crakeron/Projet_CM/Catia_GPZ500/Drawing/Drawing engrenage.jpg

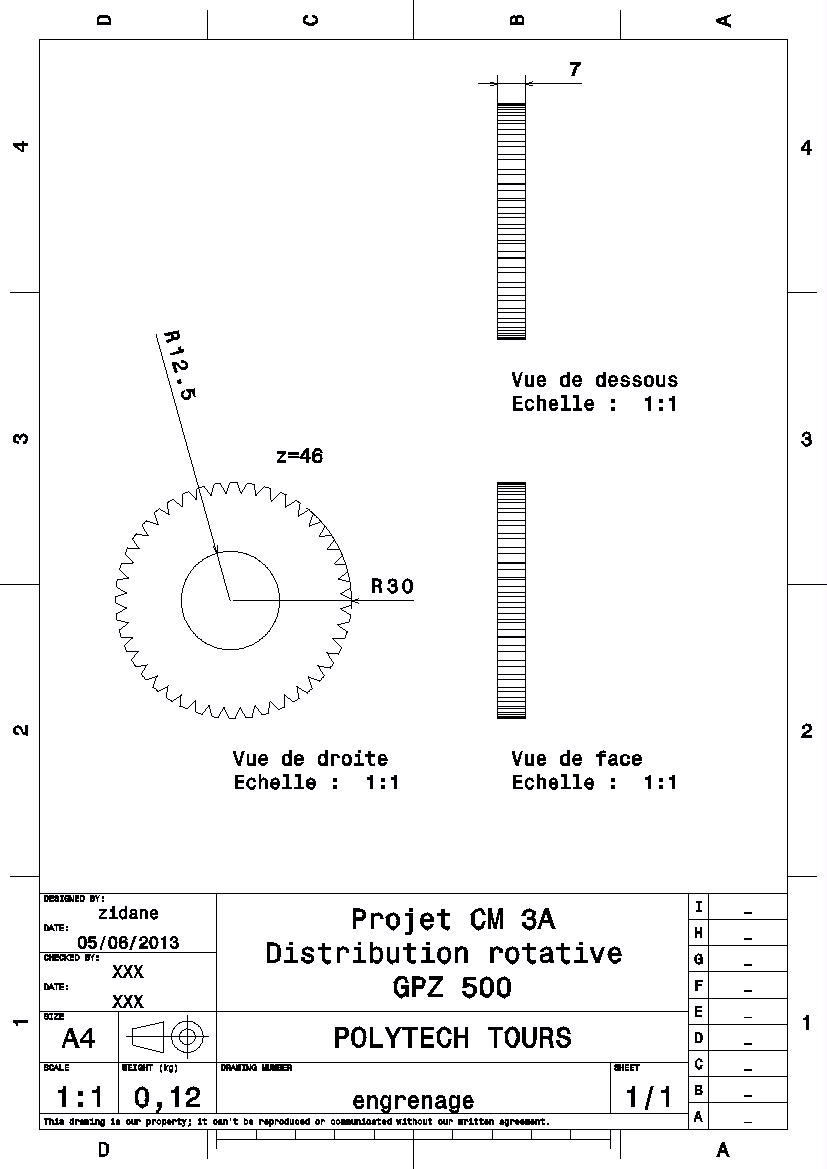
Catia_GPZ500/Drawing/Drawing engrenage.jpg
