crakeron/Projet_CM/Catia_GPZ500/Drawing/DrawingCHAPEAUX.jpg

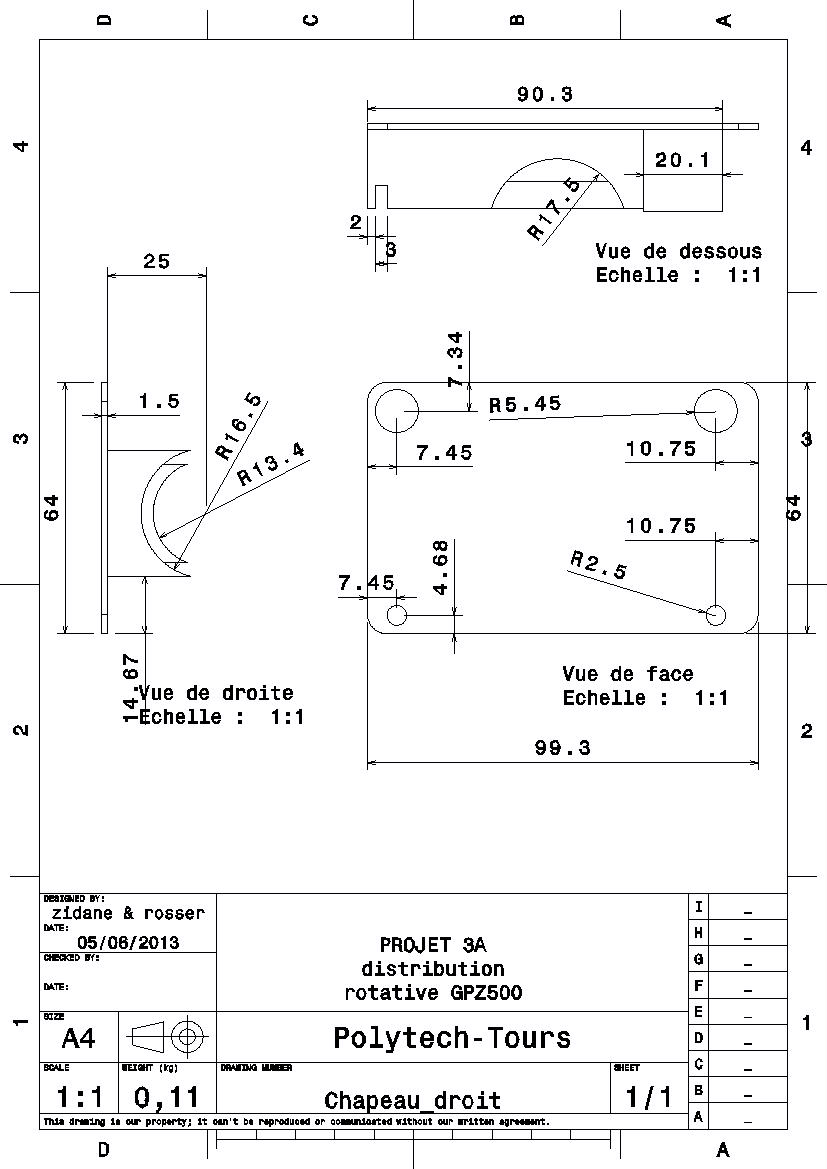
Catia_GPZ500/Drawing/DrawingCHAPEAUX.jpg
