crakeron/Projet_CM/Catia_GPZ500/Drawing/Drawingtube.jpg

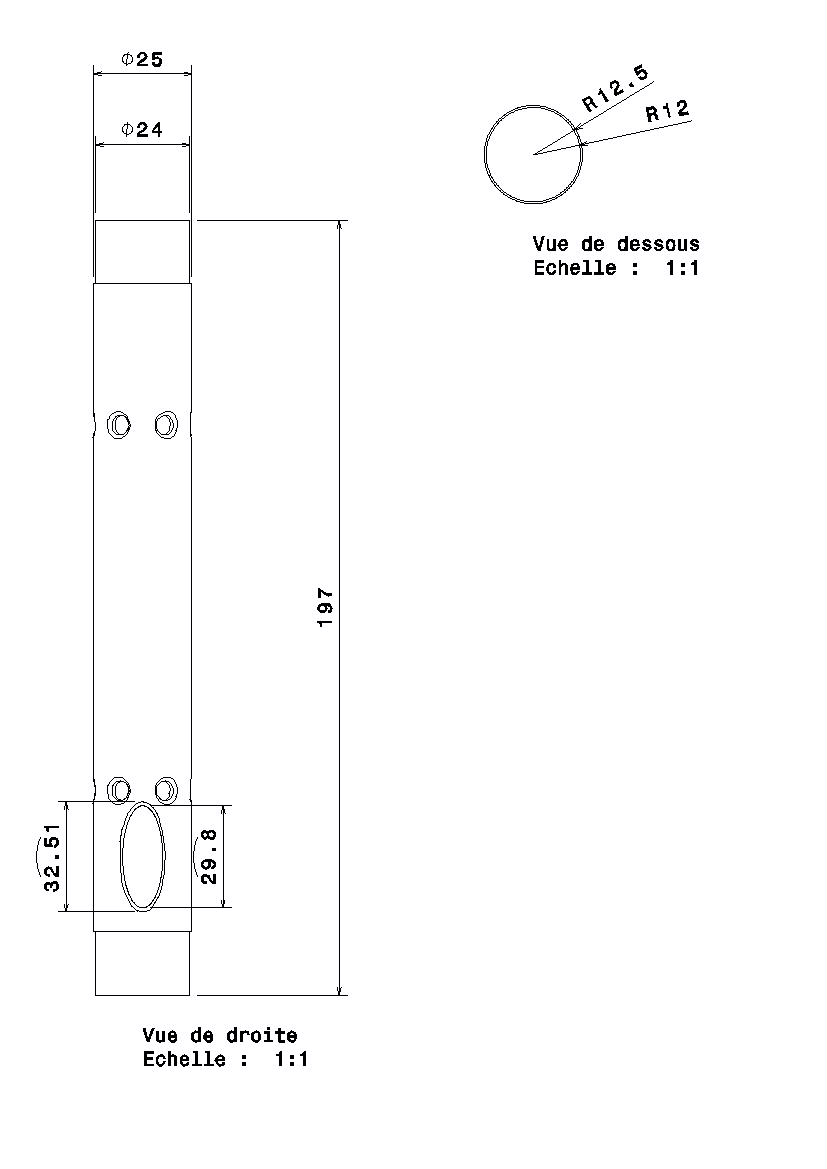
Catia_GPZ500/Drawing/Drawingtube.jpg
