crakeron/Projet_CM/Catia_GPZ500/Photos/7mai.png

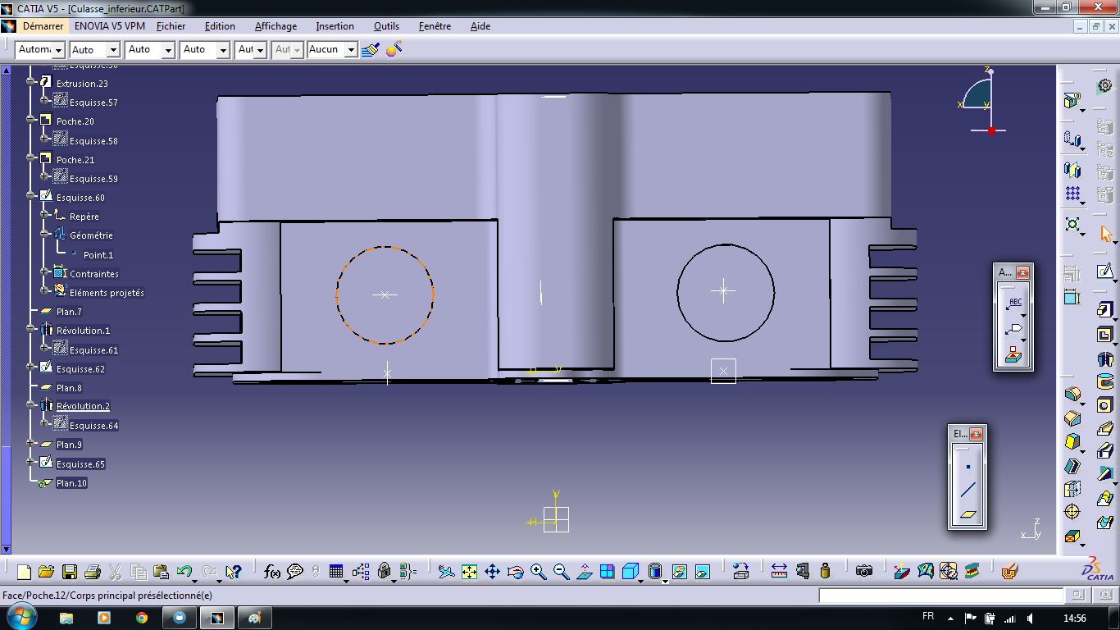
Catia_GPZ500/Photos/7mai.png
