crakeron/Projet_CM/Catia_GPZ500/Photos/7mai_2.png

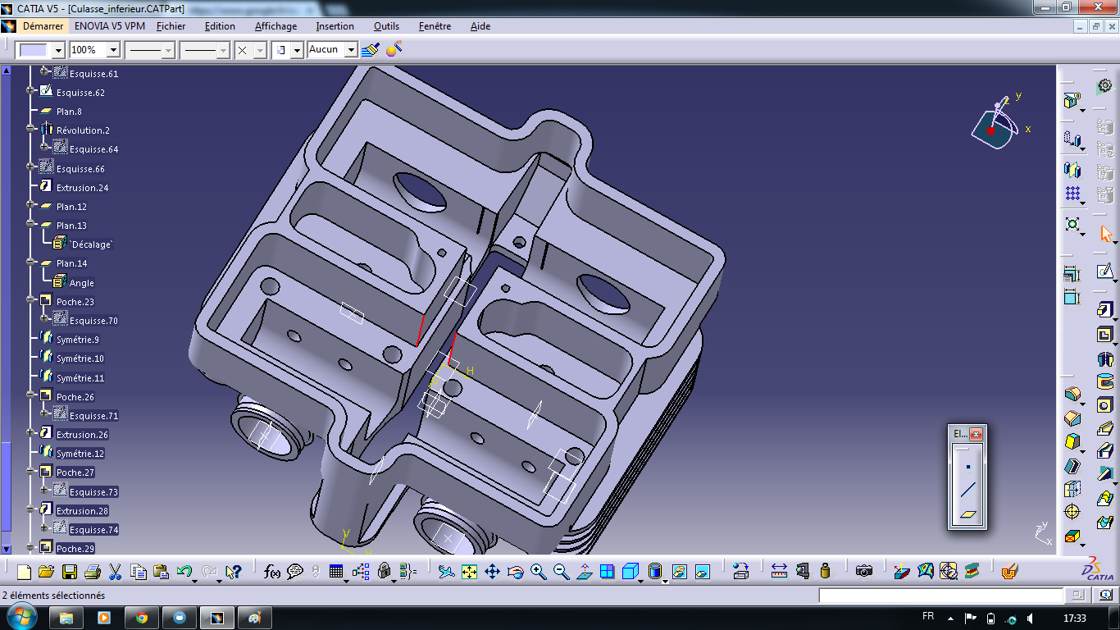
Catia_GPZ500/Photos/7mai_2.png
