crakeron/Projet_CM/Catia_GPZ500/Photos/15mai1.png

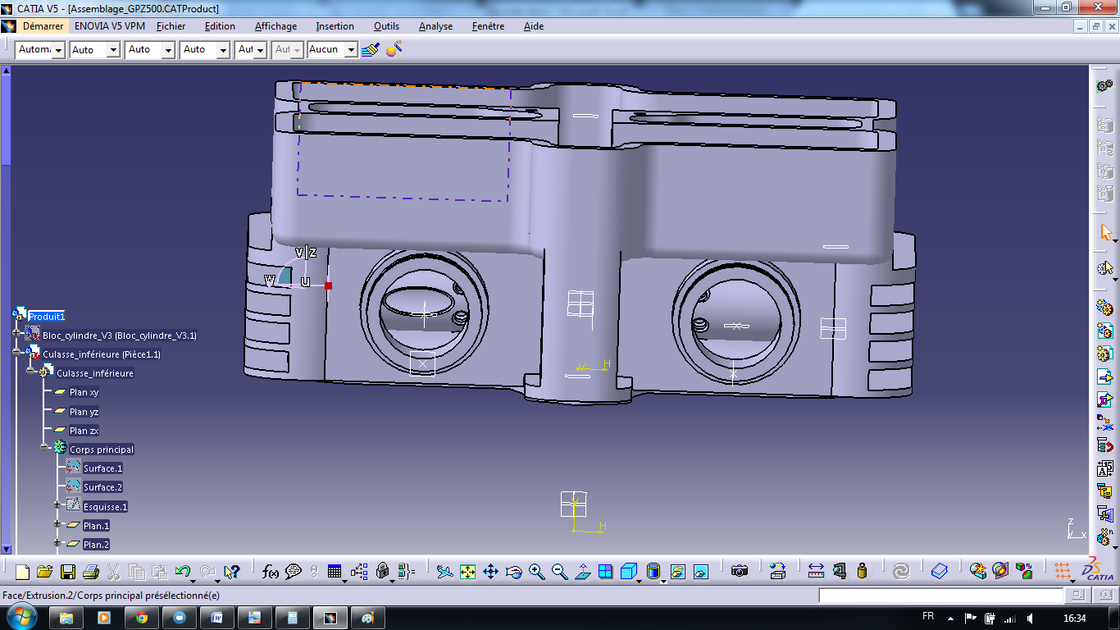
Catia_GPZ500/Photos/15mai1.png
