crakeron/Projet_CM/Catia_GPZ500/Photos/16mai2.png

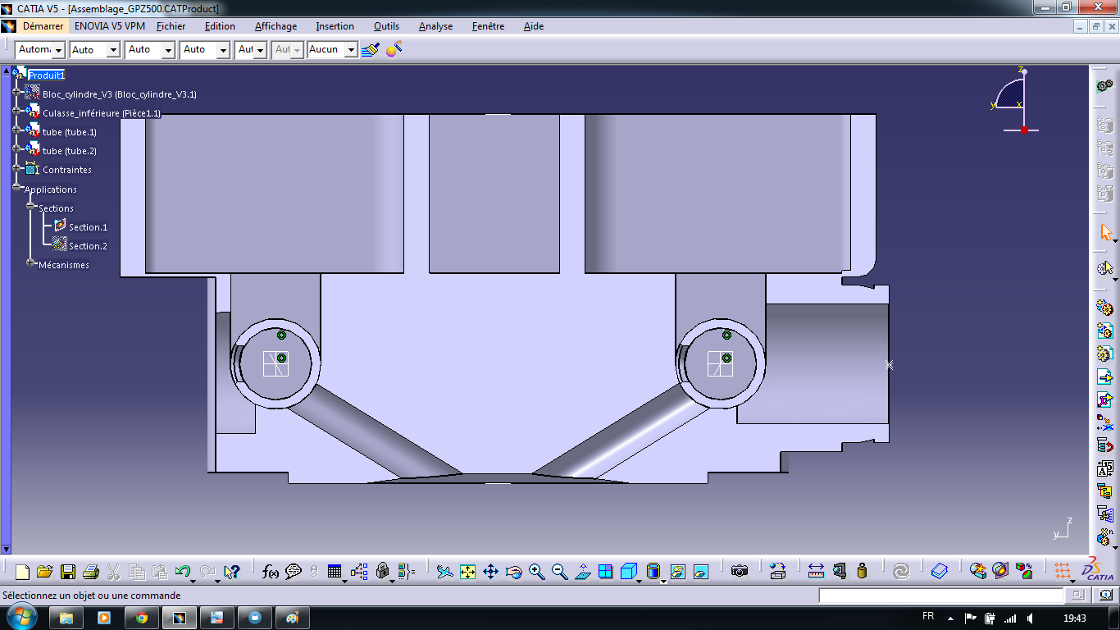
Catia_GPZ500/Photos/16mai2.png
