crakeron/Projet_CM/Catia_GPZ500/Photos/31mai1.png

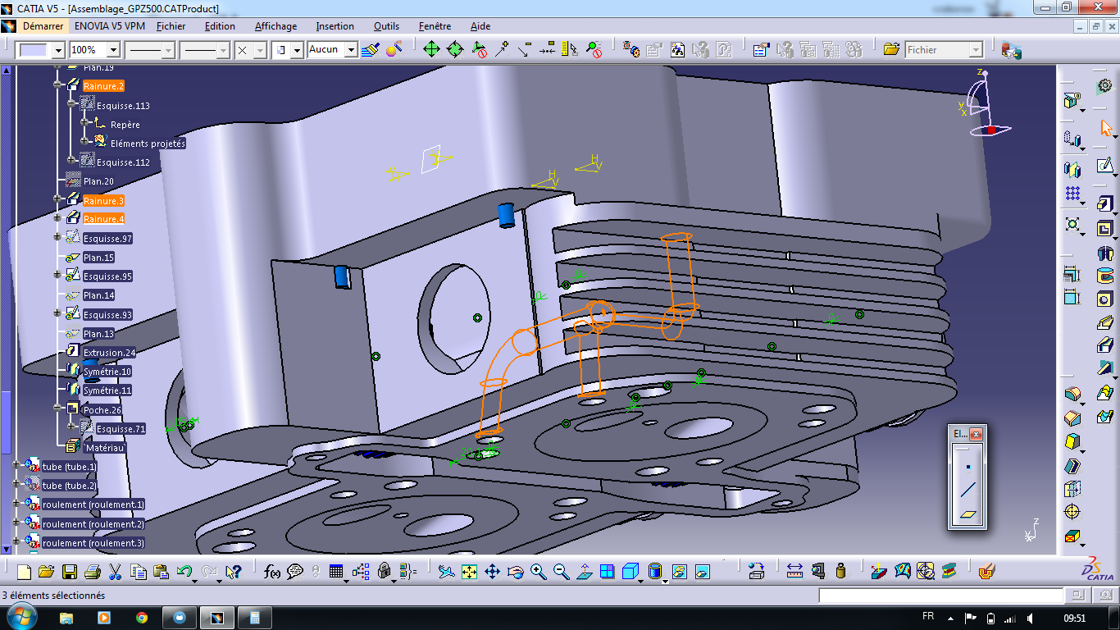
Catia_GPZ500/Photos/31mai1.png
