crakeron/Projet_CM/Catia_GPZ500/Photos/bloc cylin.bmp

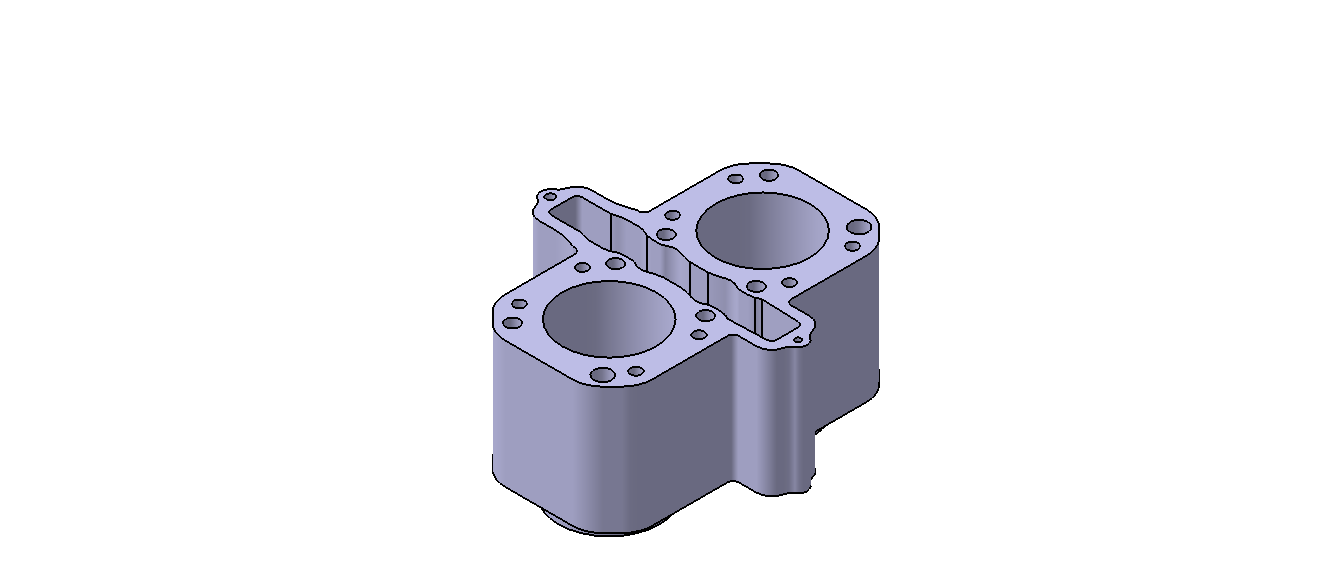
Catia_GPZ500/Photos/bloc cylin.bmp
