crakeron/Projet_CM/Catia_GPZ500/Photos/Bloc Cylindre/Bloc_Cylindre_Profil_Normale.jpg

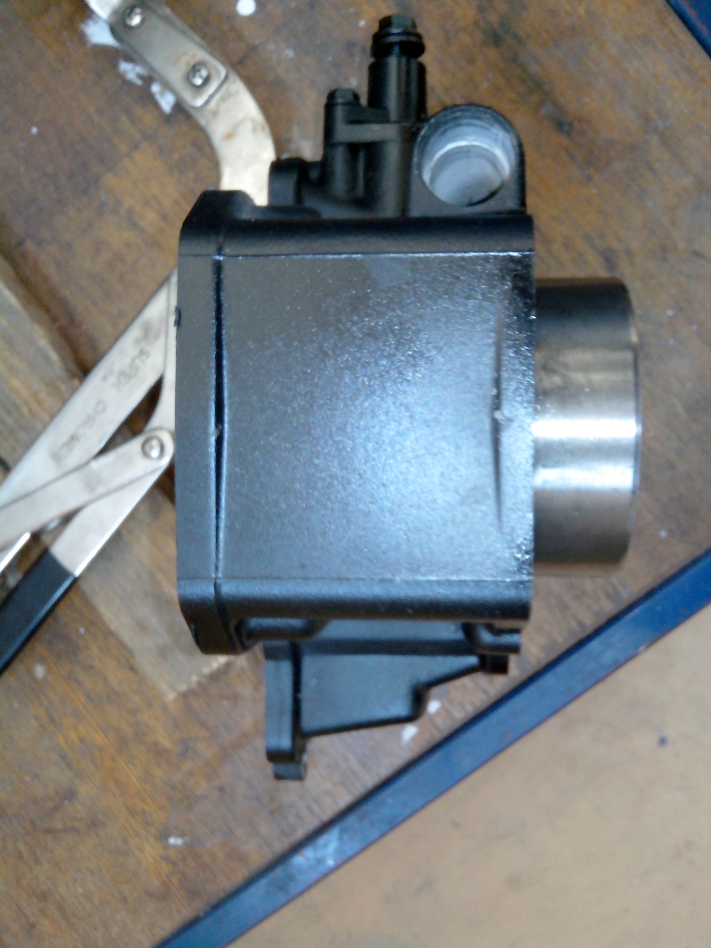
Catia_GPZ500/Photos/Bloc Cylindre/Bloc_Cylindre_Profil_Normale.jpg
