crakeron/Projet_CM/Catia_GPZ500/Photos/Bloc_cylindre cotation.jpg

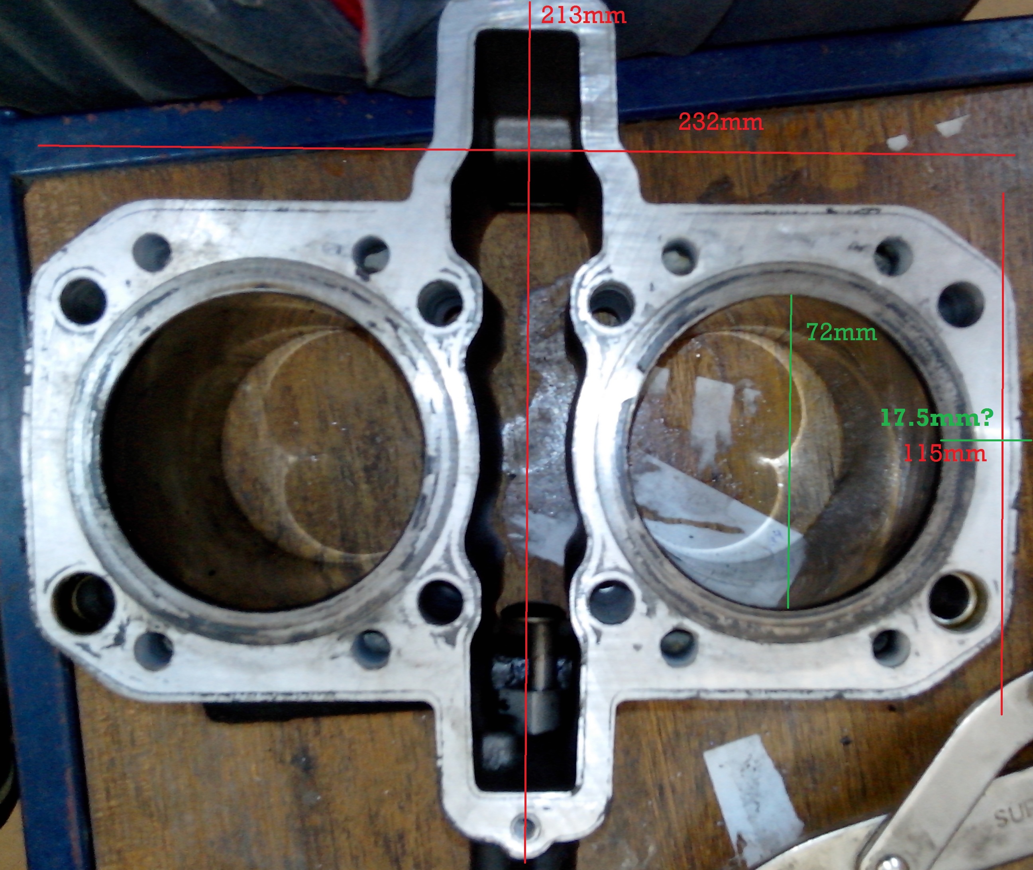
Catia_GPZ500/Photos/Bloc_cylindre cotation.jpg
