crakeron/Projet_CM/Catia_GPZ500/Photos/Culasse/Culasse_dessous.jpg

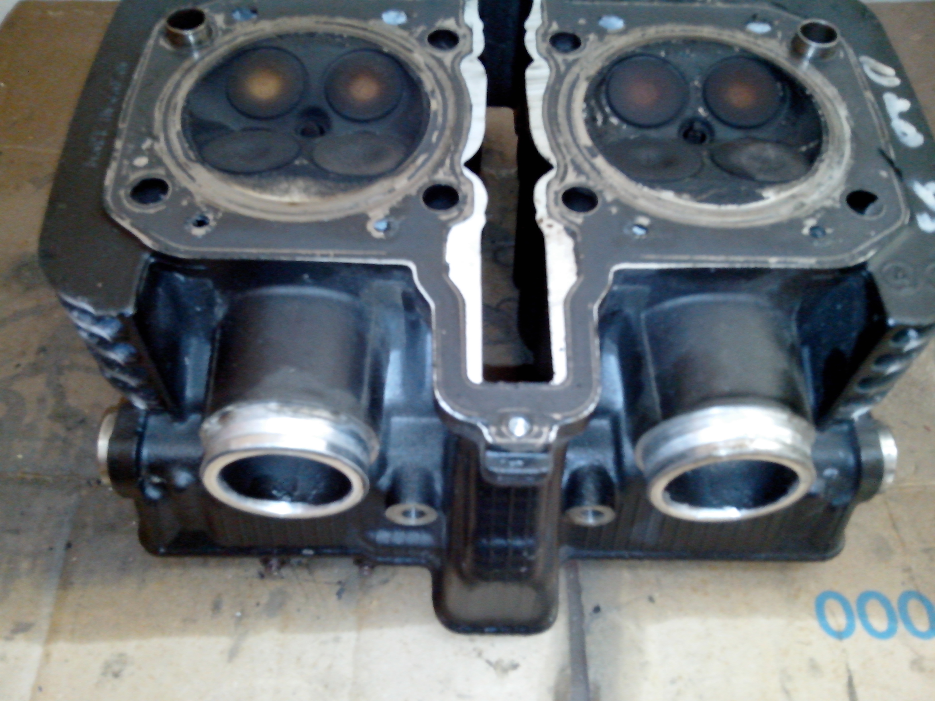
Catia_GPZ500/Photos/Culasse/Culasse_dessous.jpg
