crakeron/Projet_CM/Catia_GPZ500/Photos/Culasse/Culasse_dessous_normale.jpg

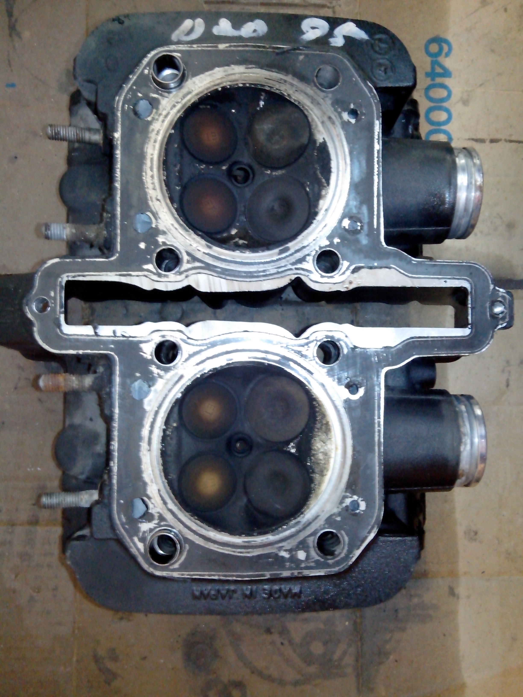
Catia_GPZ500/Photos/Culasse/Culasse_dessous_normale.jpg
