crakeron/Projet_CM/Catia_GPZ500/Photos/Culasse/Culasse_Normale.jpg

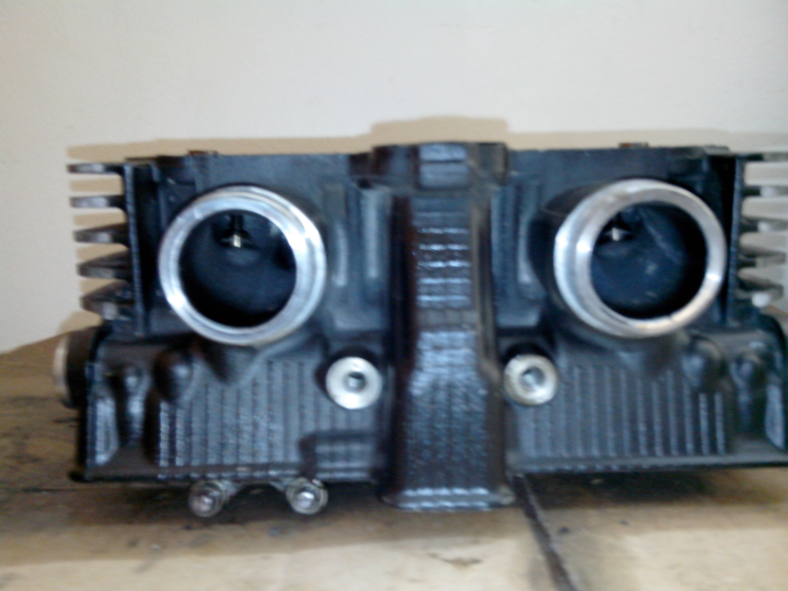
Catia_GPZ500/Photos/Culasse/Culasse_Normale.jpg
