crakeron/Projet_CM/Catia_GPZ500/Photos/engrenage.bmp

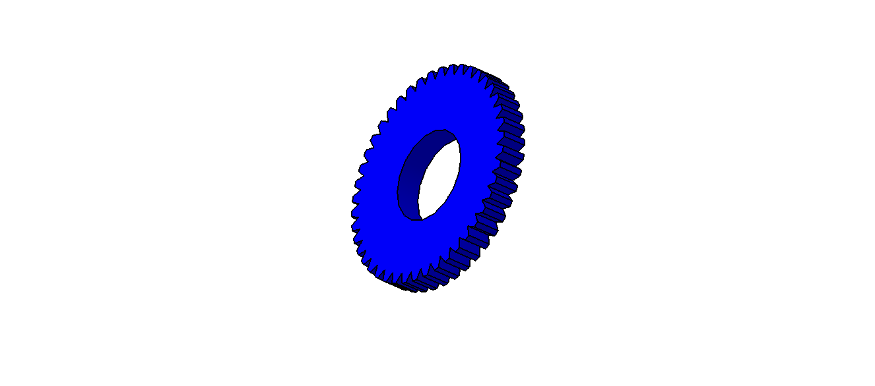
Catia_GPZ500/Photos/engrenage.bmp
