crakeron/Projet_CM/Catia_GPZ500/Photos/github.png

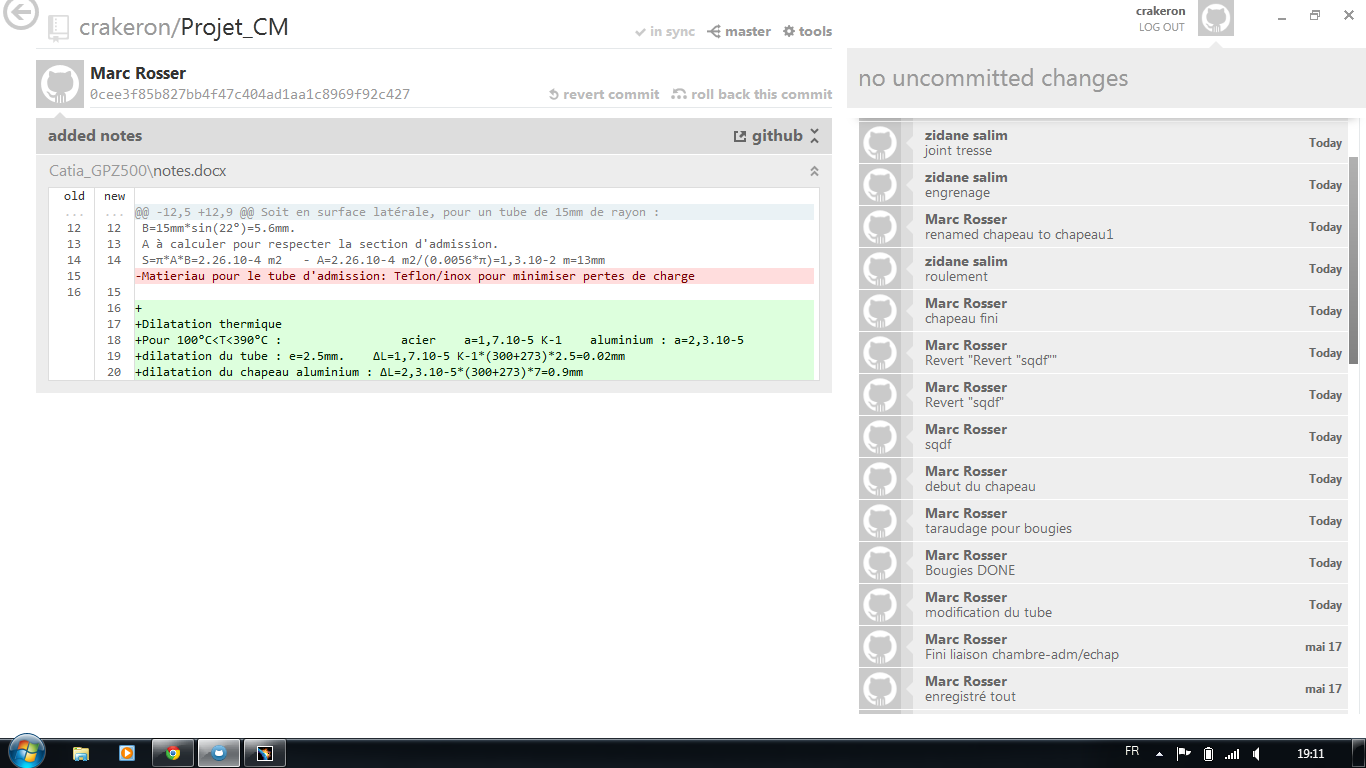
Catia_GPZ500/Photos/github.png
