crakeron/Projet_CM/Catia_GPZ500/Photos/Github_show.png

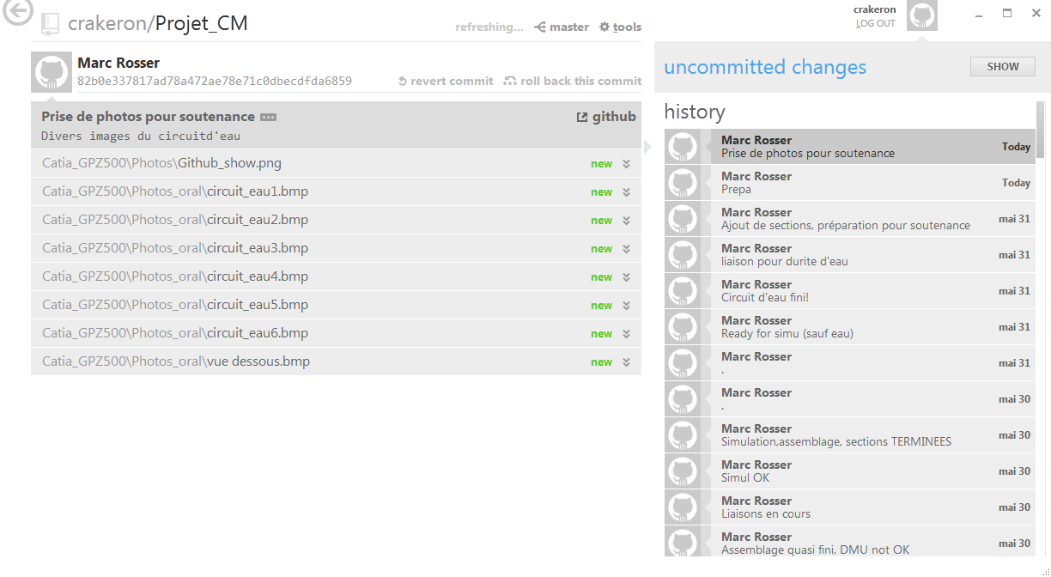
Catia_GPZ500/Photos/Github_show.png
