crakeron/Projet_CM/Catia_GPZ500/Photos/roulement.bmp

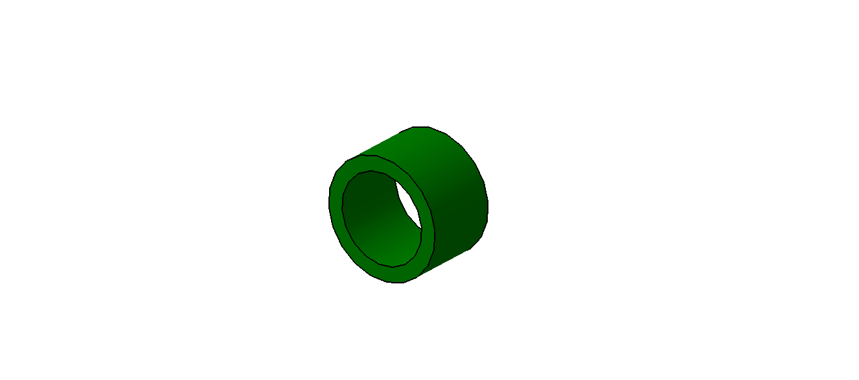
Catia_GPZ500/Photos/roulement.bmp
