crakeron/Projet_CM/Catia_GPZ500/Photos/assemblage.bmp

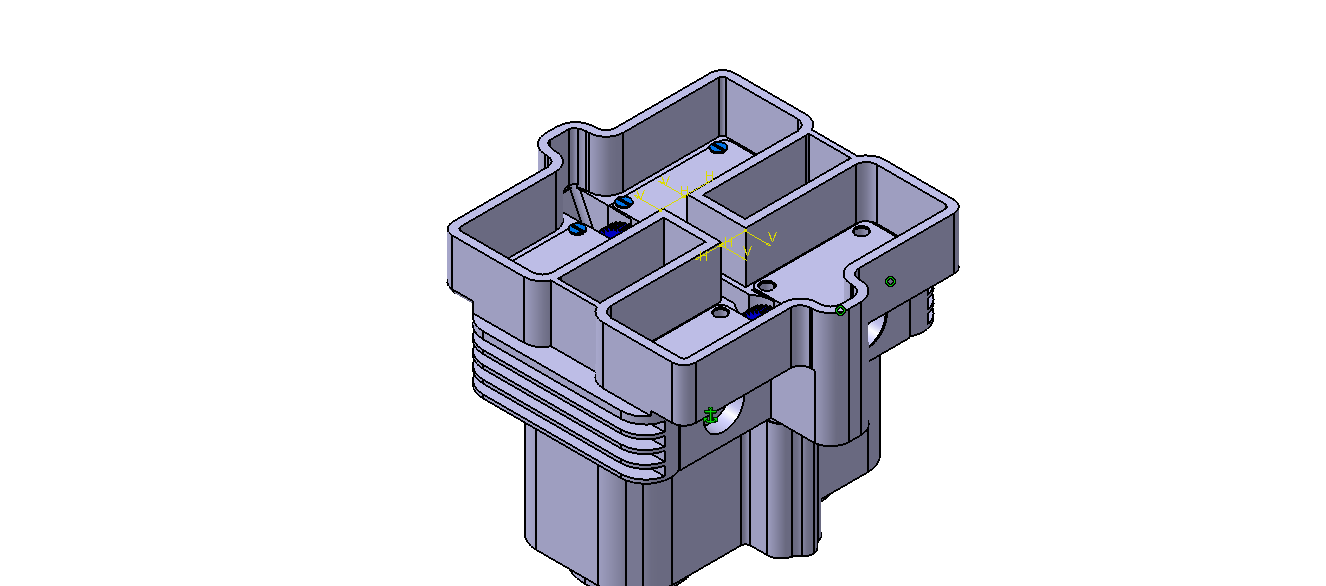
Catia_GPZ500/Photos/assemblage.bmp
